mennovf/messenger/circuit/messenger/messenger.sch

## KiCad design circuit/messenger/messenger.sch (2022-09-26)

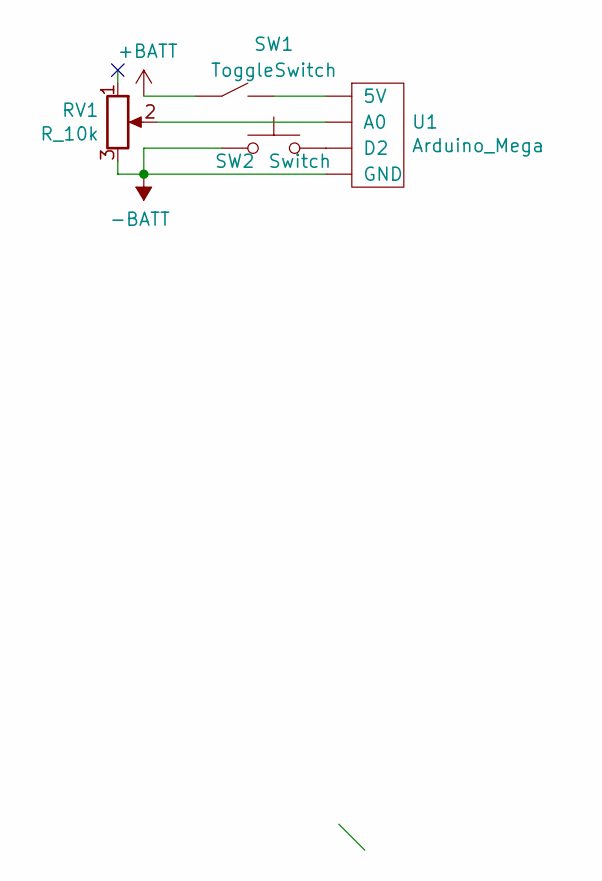
[picture p7: schematic messenger.sch]

Parts:
RV1: R_10k
SW1: ToggleSwitch
SW2: Switch
U1: Arduino_Mega

Connections:
+BATT: SW1.~
-BATT: RV1.3, SW2.1 (A), SW2.2 (A), U1.~
unnamed: RV1.2, U1.~
unnamed: SW1.~, U1.~
unnamed: SW2.3 (B), SW2.4 (B), U1.~
