mennovf/messenger/sketch/src/roboto16.cpp

/*******************************************************************************
 * Size: 16 px
 * Bpp: 4
 * Opts: --bpp 4 --size 16 --output roboto16.cpp --format lvgl --font ../../Roboto-Regular-NotoBold.ttf --range 0x2600,0x1f600,0x1f607,0x1f608,0x1f60a,0x1f60b,0x1f60c,0x1f60d,0x1f60e,0x1f60f,0x410,0x411,0xfe0f,0x414,0x415,0x417,0x1f618,0x418,0x41a,0x41b,0x41c,0x1f619,0x41e,0x41f,0x20,0x21,0x421,0x422,0x420,0x22,0x26,0x27,0x28,0x29,0x23,0x1f617,0x2c,0x2d,0x2e,0x2f,0x430,0x431,0x432,0x30,0x434,0x31,0x32,0x437,0x438,0x33,0x34,0x3b,0x35,0x36,0x37,0x38,0x39,0x3a,0x3d,0x3f,0x1f640,0x41,0x42,0x442,0x44,0x45,0x47,0x48,0x49,0x4a,0x4c,0x4d,0x4f,0x44f,0x51,0x52,0x53,0x54,0x56,0x57,0x58,0x55,0x5a,0x59,0x1f621,0x1f622,0x5e,0x5f,0x61,0x62,0x63,0x64,0x65,0x66,0x67,0x68,0x69,0x6a,0x6b,0x6c,0x6d,0x6e,0x6f,0x70,0x71,0x72,0x73,0x74,0x75,0x76,0x77,0x78,0x79,0x7a,0x1f47b,0x7e,0x1f430,0x1f495,0x1f496,0x1f497,0x1f49a,0x1f49b,0x1f49d,0x1f631,0x20ac,0xb0,0x41d,0x1f634,0x423,0x1f63d,0xe9,0xeb,0xf3,0x1f641,0x1f643,0x1f448,0x42f,0x1f90d,0x1f449,0x1f913,0x1f914,0x1f917,0x1f31e,0x433,0x1f923,0x1f924,0x1f929,0x435,0x436,0x3e,0x1f33b,0x439,0x43a,0x43b,0x43c,0x43,0x43d,0x43e,0x43f,0x46,0x440,0x2764,0x1f966,0x441,0x1f970,0x443,0x1f979,0x4b,0x1f97a,0x445,0x1f61a,0x446,0x447,0x4e,0x448,0x449,0x50,0x44b,0x44c,0x44e,0x263a,0x1f61c,0x451,0x1f61e --no-compress
 ******************************************************************************/

#ifdef LV_LVGL_H_INCLUDE_SIMPLE
#include "lvgl.h"
#else
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
    0x6, 0x96, 0x4, 0xb0, 0x2, 0xd0, 0x0, 0x36,
    0x0, 0x36, 0x0, 0xc, 0x40, 0x0, 0x99, 0x0,
    0x18, 0xcd, 0xa3, 0x0, 0x7a, 0x0, 0x0, 0xb,
    0x90, 0x0, 0x0, 0x0, 0x8, 0xc0, 0x0, 0x0,
    0x0, 0x8d, 0x72, 0x0, 0x26, 0xd9, 0x0, 0x0,
    0x0, 0x0, 0x1, 0x7b, 0xcd, 0xb7, 0x20, 0x0,
    0x0,

    /* U+1F97A "🥺" */
    0x0, 0x0, 0x1, 0x7b, 0xcd, 0xb7, 0x20, 0x0,
    0x0, 0x0, 0x0, 0x8d, 0x72, 0x0, 0x26, 0xd9,
    0x0, 0x0, 0x0, 0xb, 0x90, 0x0, 0x0, 0x0,
    0x8, 0xc0, 0x0, 0x0, 0x99, 0x0, 0x0, 0x0,
    0x0, 0x10, 0x7a, 0x0, 0x2, 0xd0, 0x4c, 0x90,
    0x0, 0x1, 0xc5, 0xc, 0x40, 0x9, 0x63, 0x83,
    0x0, 0x0, 0x0, 0x17, 0x44, 0xb0, 0xe, 0x10,
    0x37, 0x82, 0x0, 0x6, 0x95, 0x0, 0xe0, 0xe,
    0x3, 0x60, 0x3e, 0x20, 0x81, 0x5f, 0x50, 0xc2,
    0x1d, 0x9, 0x41, 0xbf, 0x70, 0xd1, 0xbf, 0xb0,
    0xb3, 0xe, 0x7, 0xff, 0x9f, 0x50, 0xdf, 0xfb,
    0x90, 0xc2, 0xe, 0x10, 0xbf, 0xf9, 0x0, 0x3f,
    0xfd, 0x10, 0xe0, 0x9, 0x60, 0x2, 0x10, 0x0,
    0x0, 0x20, 0x4, 0xb0, 0x2, 0xd0, 0x0, 0x0,
    0x0, 0x0, 0x0, 0xc, 0x40, 0x0, 0x99, 0x0,
    0x5, 0xdd, 0xc0, 0x0, 0x7a, 0x0, 0x0, 0xb,
    0x90, 0x0, 0x0, 0x0, 0x8, 0xc0, 0x0, 0x0,
    0x0, 0x8d, 0x72, 0x0, 0x26, 0xd9, 0x0, 0x0,
    0x0, 0x0, 0x1, 0x7b, 0xcd, 0xb7, 0x20, 0x0,
    0x0
};


/*---------------------
 *  GLYPH DESCRIPTION
 *--------------------*/

static const lv_font_fmt_txt_glyph_dsc_t glyph_dsc[] = {
    {.bitmap_index = 0, .adv_w = 0, .box_w = 0, .box_h = 0, .ofs_x = 0, .ofs_y = 0} /* id = 0 reserved */,
    {.bitmap_index = 0, .adv_w = 63, .box_w = 0, .box_h = 0, .ofs_x = 0, .ofs_y = 0},
    {.bitmap_index = 0, .adv_w = 66, .box_w = 2, .box_h = 12, .ofs_x = 1, .ofs_y = 0},
    {.bitmap_index = 12, .adv_w = 82, .box_w = 4, .box_h = 5, .ofs_x = 1, .ofs_y = 7},
    {.bitmap_index = 22, .adv_w = 158, .box_w = 10, .box_h = 12, .ofs_x = 0, .ofs_y = 0},
    {.bitmap_index = 82, .adv_w = 159, .box_w = 10, .box_h = 12, .ofs_x = 0, .ofs_y = 0},
    {.bitmap_index = 142, .adv_w = 45, .box_w = 2, .box_h = 4, .ofs_x = 0, .ofs_y = 8},
    {.bitmap_index = 146, .adv_w = 88, .box_w = 5, .box_h = 18, .ofs_x = 1, .ofs_y = -4},
    {.bitmap_index = 191, .adv_w = 89, .box_w = 5, .box_h = 18, .ofs_x = 0, .ofs_y = -4},
    {.bitmap_index = 236, .adv_w = 50, .box_w = 3, .box_h = 5, .ofs_x = 0, .ofs_y = -3},
    {.bitmap_index = 244, .adv_w = 71, .box_w = 5, .box_h = 3, .ofs_x = 0, .ofs_y = 4},
    {.bitmap_index = 252, .adv_w = 67, .box_w = 2, .box_h = 2, .ofs_x = 1, .ofs_y = 0},
    {.bitmap_index = 254, .adv_w = 106, .box_w = 7, .box_h = 13, .ofs_x = 0, .ofs_y = -1},
    {.bitmap_index = 300, .adv_w = 144, .box_w = 9, .box_h = 12, .ofs_x = 0, .ofs_y = 0},
    {.bitmap_index = 354, .adv_w = 144, .box_w = 5, .box_h = 12, .ofs_x = 1, .ofs_y = 0},
    {.bitmap_index = 384, .adv_w = 144, .box_w = 9, .box_h = 12, .ofs_x = 0, .ofs_y = 0},
    {.bitmap_index = 438, .adv_w = 144, .box_w = 8, .box_h = 12, .ofs_x = 0, .ofs_y = 0},
    {.bitmap_index = 486, .adv_w = 144, .box_w = 9, .box_h = 12, .ofs_x = 0, .ofs_y = 0},
    {.bitmap_index = 540, .adv_w = 144, .box_w = 8, .box_h = 12, .ofs_x = 1, .ofs_y = 0},
    {.bitmap_index = 588, .adv_w = 144, .box_w = 8, .box_h = 12, .ofs_x = 1, .ofs_y = 0},
    {.bitmap_index = 636, .adv_w = 144, .box_w = 9, .box_h = 12, .ofs_x = 0, .ofs_y = 0},
    {.bitmap_index = 690, .adv_w = 144, .box_w = 9, .box_h = 12, .ofs_x = 0, .ofs_y = 0},
    {.bitmap_index = 744, .adv_w = 144, .box_w = 8, .box_h = 12, .ofs_x = 0, .ofs_y = 0},
    {.bitmap_index = 792, .adv_w = 62, .box_w = 2, .box_h = 9, .ofs_x = 1, .ofs_y = 0},
    {.bitmap_index = 801, .adv_w = 54, .box_w = 3, .box_h = 12, .ofs_x = 0, .ofs_y = -3},
    {.bitmap_index = 819, .adv_w = 141, .box_w = 7, .box_h = 6, .ofs_x = 1, .ofs_y = 3},
    {.bitmap_index = 840, .adv_w = 134, .box_w = 7, .box_h = 8, .ofs_x = 1, .ofs_y = 1},
    {.bitmap_index = 868, .adv_w = 121, .box_w = 7, .box_h = 12, .ofs_x = 0, .ofs_y = 0},
    {.bitmap_index = 910, .adv_w = 167, .box_w = 11, .box_h = 12, .ofs_x = 0, .ofs_y = 0},
    {.bitmap_index = 976, .adv_w = 159, .box_w = 9, .box_h = 12, .ofs_x = 1, .ofs_y = 0},
    {.bitmap_index = 1030, .adv_w = 167, .box_w = 10, .box_h = 12, .ofs_x = 0, .ofs_y = 0},
    {.bitmap_index = 1090, .adv_w = 168, .box_w = 9, .box_h = 12, .ofs_x = 1, .ofs_y = 0},
    {.bitmap_index = 1144, .adv_w = 146, .box_w = 8, .box_h = 12, .ofs_x = 1, .ofs_y = 0},
    {.bitmap_index = 1192, .adv_w = 142, .box_w = 8, .box_h = 12, .ofs_x = 1, .ofs_y = 0},
    {.bitmap_index = 1240, .adv_w = 174, .box_w = 10, .box_h = 12, .ofs_x = 0, .ofs_y = 0},
    {.bitmap_index = 1300, .adv_w = 183, .box_w = 10, .box_h = 12, .ofs_x = 1, .ofs_y = 0},
    {.bitmap_index = 1360, .adv_w = 70, .box_w = 2, .box_h = 12, .ofs_x = 1, .ofs_y = 0},
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
    {.bitmap_index = 12580, .adv_w = 325, .box_w = 18, .box_h = 17, .ofs_x = 1, .ofs_y = -3},
    {.bitmap_index = 12733, .adv_w = 325, .box_w = 18, .box_h = 17, .ofs_x = 1, .ofs_y = -3},
    {.bitmap_index = 12886, .adv_w = 325, .box_w = 17, .box_h = 17, .ofs_x = 2, .ofs_y = -3},
    {.bitmap_index = 13031, .adv_w = 325, .box_w = 20, .box_h = 19, .ofs_x = 0, .ofs_y = -4},
    {.bitmap_index = 13221, .adv_w = 325, .box_w = 18, .box_h = 17, .ofs_x = 1, .ofs_y = -3},
    {.bitmap_index = 13374, .adv_w = 325, .box_w = 18, .box_h = 17, .ofs_x = 1, .ofs_y = -3}
};

/*---------------------
 *  CHARACTER MAPPING
 *--------------------*/

static const uint8_t glyph_id_ofs_list_0[] = {
    0, 1, 2, 3, 0, 0, 4, 5,
    6, 7, 0, 0, 8, 9, 10, 11,
    12, 13, 14, 15, 16, 17, 18, 19,
    20, 21, 22, 23, 0, 24, 25, 26,
    0, 27, 28, 29, 30, 31, 32, 33,
    34, 35, 36, 37, 38, 39, 40, 41,
    42, 43, 44, 45, 46, 47, 48, 49,
    50, 51, 52, 0, 0, 0, 53, 54
};

static const uint16_t unicode_list_2[] = {
    0x0, 0x32, 0x6b, 0x6d, 0x75, 0x392, 0x393, 0x396,
    0x397, 0x399, 0x39a
};

static const uint16_t unicode_list_5[] = {
    0x0, 0x1, 0x2, 0x3, 0x4, 0x6, 0x7, 0x9,
    0xa, 0xc, 0x1c67, 0x21bb, 0x21f5, 0x231f
};

static const uint16_t unicode_list_6[] = {
    0x0, 0xf50f, 0xf52c, 0xf621, 0xf639, 0xf63a, 0xf66c, 0xf686,
    0xf687, 0xf688, 0xf68b, 0xf68c, 0xf68e, 0xf7f1, 0xf7f8, 0xf7f9,
    0xf7fb, 0xf7fc, 0xf7fd, 0xf7fe, 0xf7ff, 0xf800, 0xf808, 0xf809,
    0xf80a, 0xf80b, 0xf80d, 0xf80f, 0xf812, 0xf813, 0xf822, 0xf825,
    0xf82e, 0xf831, 0xf832, 0xf834, 0xfafe, 0xfb04, 0xfb05, 0xfb08,
    0xfb14, 0xfb15, 0xfb1a, 0xfb57, 0xfb61, 0xfb6a, 0xfb6b
};

/*Collect the unicode lists and glyph_id offsets*/
static const lv_font_fmt_txt_cmap_t cmaps[] =
{
    {
        .range_start = 32, .range_length = 64, .glyph_id_start = 1,
        .unicode_list = NULL, .glyph_id_ofs_list = glyph_id_ofs_list_0, .list_length = 64, .type = LV_FONT_FMT_TXT_CMAP_FORMAT0_FULL
    },
    {
        .range_start = 97, .range_length = 26, .glyph_id_start = 56,
        .unicode_list = NULL, .glyph_id_ofs_list = NULL, .list_length = 0, .type = LV_FONT_FMT_TXT_CMAP_FORMAT0_TINY
    },
    {
        .range_start = 126, .range_length = 923, .glyph_id_start = 82,
        .unicode_list = unicode_list_2, .glyph_id_ofs_list = NULL, .list_length = 11, .type = LV_FONT_FMT_TXT_CMAP_SPARSE_TINY
    },
    {
        .range_start = 1050, .range_length = 10, .glyph_id_start = 93,
        .unicode_list = NULL, .glyph_id_ofs_list = NULL, .list_length = 0, .type = LV_FONT_FMT_TXT_CMAP_FORMAT0_TINY
    },
    {
        .range_start = 1071, .range_length = 21, .glyph_id_start = 103,
        .unicode_list = NULL, .glyph_id_ofs_list = NULL, .list_length = 0, .type = LV_FONT_FMT_TXT_CMAP_FORMAT0_TINY
    },
    {
        .range_start = 1093, .range_length = 8992, .glyph_id_start = 124,
        .unicode_list = unicode_list_5, .glyph_id_ofs_list = NULL, .list_length = 14, .type = LV_FONT_FMT_TXT_CMAP_SPARSE_TINY
    },
    {
        .range_start = 65039, .range_length = 64364, .glyph_id_start = 138,
        .unicode_list = unicode_list_6, .glyph_id_ofs_list = NULL, .list_length = 47, .type = LV_FONT_FMT_TXT_CMAP_SPARSE_TINY
    }
};

/*-----------------
 *    KERNING
 *----------------*/


/*Map glyph_ids to kern left classes*/
static const uint8_t kern_left_class_mapping[] PROGMEM =
{
    0, 1, 0, 2, 0, 0, 2, 3,
    0, 4, 0, 4, 5, 0, 0, 0,
    0, 0, 0, 0, 0, 0, 0, 0,
    0, 0, 0, 0, 6, 7, 8, 9,
    10, 11, 0, 12, 12, 13, 14, 15,
    12, 12, 9, 16, 17, 18, 0, 19,
    13, 20, 21, 22, 23, 24, 0, 0,
    25, 26, 27, 0, 28, 29, 0, 30,
    0, 0, 31, 0, 30, 30, 32, 26,
    0, 33, 0, 34, 0, 35, 36, 37,
    35, 38, 0, 0, 28, 28, 32, 6,
    39, 40, 10, 41, 12, 14, 12, 12,
    12, 9, 0, 16, 8, 19, 42, 43,
    25, 44, 45, 46, 47, 28, 37, 27,
    0, 0, 48, 0, 0, 0, 32, 0,
    26, 27, 49, 35, 37, 50, 0, 0,
    51, 0, 52, 53, 0, 28, 0, 0,
    0, 0, 0, 0, 0, 0, 0, 0,
    0, 0, 0, 0, 0, 0, 0, 0,
    0, 0, 0, 0, 0, 0, 0, 0,
    0, 0, 0, 0, 0, 0, 0, 0,
    0, 0, 0, 0, 0, 0, 0, 0,
    0, 0, 0, 0, 0, 0, 0, 0,
    0
};

/*Map glyph_ids to kern right classes*/
static const uint8_t kern_right_class_mapping[] PROGMEM =
{
    0, 1, 0, 2, 0, 3, 2, 0,
    4, 5, 6, 5, 7, 0, 0, 0,
    0, 0, 0, 0, 8, 0, 0, 0,
    0, 0, 0, 9, 10, 0, 11, 0,
    0, 0, 11, 0, 0, 12, 0, 0,
    0, 0, 11, 0, 11, 0, 13, 14,
    15, 16, 17, 18, 19, 20, 0, 0,
    21, 0, 22, 22, 22, 23, 22, 0,
    0, 0, 0, 0, 24, 24, 25, 24,
    22, 26, 27, 28, 29, 30, 31, 32,
    30, 33, 0, 0, 22, 22, 25, 10,
    0, 34, 0, 0, 0, 0, 35, 0,
    0, 11, 0, 0, 11, 14, 36, 0,
    21, 37, 38, 24, 39, 22, 32, 40,
    24, 24, 24, 41, 24, 24, 25, 24,
    24, 22, 42, 30, 32, 24, 43, 24,
    24, 44, 24, 24, 45, 22, 0, 0,
    0, 0, 0, 0, 0, 0, 0, 0,
    0, 0, 0, 0, 0, 0, 0, 0,
    0, 0, 0, 0, 0, 0, 0, 0,
    0, 0, 0, 0, 0, 0, 0, 0,
    0, 0, 0, 0, 0, 0, 0, 0,
    0, 0, 0, 0, 0, 0, 0, 0,
    0
};

/*Kern values between classes*/
static const int8_t kern_class_values[] PROGMEM =
{
    0, 0, 0, 0, 0, 0, 0, 0,
    0, 0, 0, 0, 0, -5, 0, 0,
    0, 0, 0, 0, 0, 0, 0, 0,
    0, 0, 0, 0, 0, 0, 0, 0,
    0, 0, 0, 0, 0, 0, 0, 0,
    0, 0, 0, 0, 0, 0, -13, 0,
    0, 0, 0, 0, 0, 0, -15, 0,
    0, 0, 0, 0, 0, 0, 0, 0,
    0, -6, -7, 0, -2, -8, 0, -10,
    0, 0, 0, 1, 0, 0, 0, 0,
    0, 0, 0, 0, 0, 0, 0, 0,
    0, 0, 0, 0, 0, 0, 0, 0,
    0, 0, 0, 0, 0, 0, 0, 0,
    0, 3, 2, 0, 3, 0, 0, 0,
    0, 0, 0, 0, 0, 0, 0, 0,
    0, 0, 0, 0, 0, 0, 0, 0,
    0, 0, 0, 0, 0, 0, 0, 0,
    -21, 0, 0, 0, 0, 0, 0, 0,
    0, 0, 0, 0, 0, 0, 0, 0,
    0, 0, 0, 0, 0, 0, 0, 0,
    0, 0, 0, 0, 0, 0, 0, 0,
    0, 0, 0, 0, 0, 0, 0, 0,
    0, 0, 0, 0, 0, 0, 0, 0,
    0, 0, -28, 0, 0, 0, 0, 0,
    0, 0, 0, 0, 0, 0, 0, 0,
    0, 0, 0, 0, 0, 0, 0, 0,
    0, 0, 0, 0, 0, 0, 0, 0,
    0, 0, 0, 0, 0, 0, 0, 0,
    0, 0, -15, 0, 0, 0, 0, 0,
    0, -8, 0, -1, 0, 0, -16, -2,
    -11, -9, 0, -12, 0, 0, 0, 0,
    0, -1, 0, 0, -2, -1, -6, -4,
    0, 2, 2, 2, 0, 0, 0, 0,
    0, 2, -7, -14, 0, 0, 0, 0,
    0, 0, 0, 0, 0, 0, 0, 0,
    0, 0, 0, -3, 0, -3, 0, 0,
    -7, 0, 0, 0, 0, 0, 0, 0,
    0, 0, 0, 0, 0, 0, 0, 0,
    0, -2, 0, 0, 0, 0, 0, 0,
    0, 0, 0, 0, 0, 0, -3, 0,
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
};


/*Collect the kern class' data in one place*/
static const lv_font_fmt_txt_kern_classes_t kern_classes =
{
    .class_pair_values   = kern_class_values,
    .left_class_mapping  = kern_left_class_mapping,
    .right_class_mapping = kern_right_class_mapping,
    .left_class_cnt      = 53,
    .right_class_cnt     = 45,
};

/*--------------------
 *  ALL CUSTOM DATA
 *--------------------*/

/*Store all the custom data of the font*/
static lv_font_fmt_txt_dsc_t font_dsc = {
    .glyph_bitmap = glyph_bitmap,
    .glyph_dsc = glyph_dsc,
    .cmaps = cmaps,
    .kern_dsc = &kern_classes,
    .kern_scale = 16,
    .cmap_num = 7,
    .bpp = 4,
    .kern_classes = 1,
    .bitmap_format = 0,
};


/*-----------------
 *  PUBLIC FONT
 *----------------*/

/*Initialize a public general font descriptor*/
lv_font_t roboto16 = {
    .get_glyph_dsc = lv_font_get_glyph_dsc_fmt_txt,    /*Function pointer to get glyph's data*/
    .get_glyph_bitmap = lv_font_get_bitmap_fmt_txt,    /*Function pointer to get glyph's bitmap*/
    .line_height = 19,          /*The maximum line height required by the font*/
    .base_line = 4,             /*Baseline measured from the bottom of the line*/
    .subpx = LV_FONT_SUBPX_NONE,
    .dsc = &font_dsc           /*The custom font data. Will be accessed by `get_glyph_bitmap/dsc` */
};



#endif /*#if ROBOTO16*/
